Acmex2564/Z31-FLCU/ex_IMG_20210104_2122084.jpg

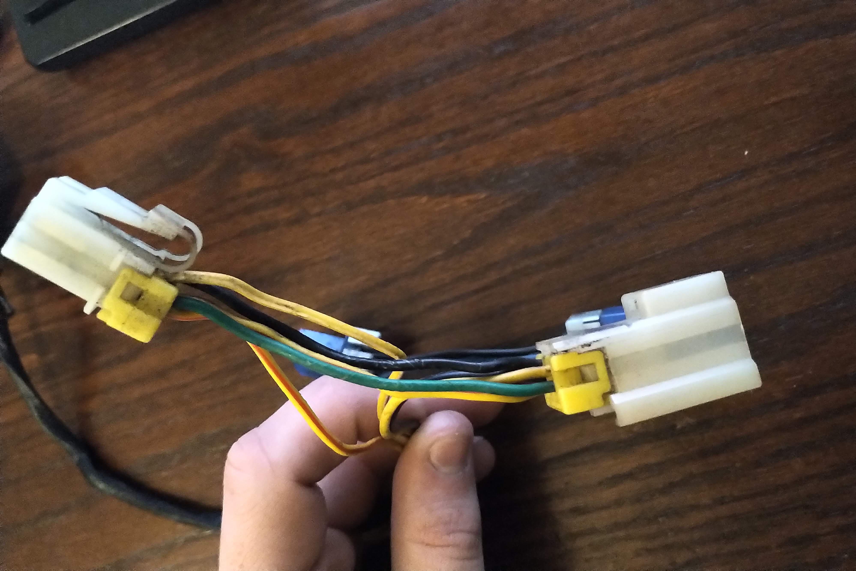
ex_IMG_20210104_2122084.jpg
