Acmex2564/Z31-FLCU/ex_Untitled.png

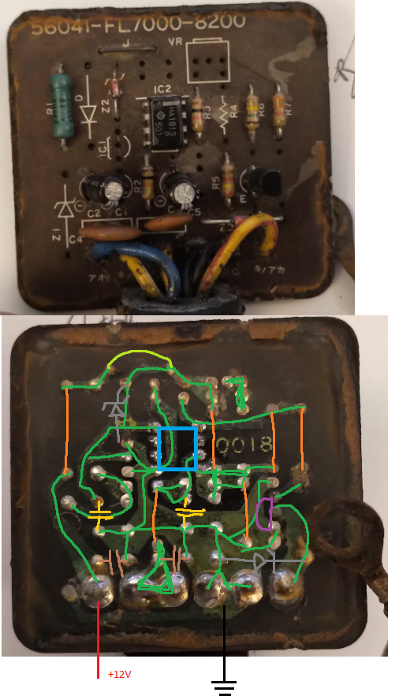
ex_Untitled.png
